ice458/pico_synthesizer/pitch_bend_table_interpolated.h

#ifndef PITCH_BEND_TABLE_INTERPOLATED_H
#define PITCH_BEND_TABLE_INTERPOLATED_H

#include "fp.h"

#define PITCH_BEND_INTERPOLATED_TABLE_SIZE 256
#define PITCH_BEND_ORIGINAL_TABLE_SIZE 16384

// Pitch bend factors (interpolated): Q8 format
// 2D Array: pitch_bend_factors_interpolated[max_semitones_0_to_24][bend_value_0_to_255]
// Dimensions: [25][256]
static const q8_t pitch_bend_factors_interpolated[25][256] = {
    { // Table for +/- 0 semitones
        256, 256, 256, 256, 256, 256, 256, 256, 
        256, 256, 256, 256, 256, 256, 256, 256, 
        256, 256, 256, 256, 256, 256, 256, 256, 
        256, 256, 256, 256, 256, 256, 256, 256, 
        256, 256, 256, 256, 256, 256, 256, 256, 
        256, 256, 256, 256, 256, 256, 256, 256, 
        256, 256, 256, 256, 256, 256, 256, 256, 
        256, 256, 256, 256, 256, 256, 256, 256, 
        256, 256, 256, 256, 256, 256, 256, 256, 
        256, 256, 256, 256, 256, 256, 256, 256, 
        256, 256, 256, 256, 256, 256, 256, 256, 
        256, 256, 256, 256, 256, 256, 256, 256, 
        256, 256, 256, 256, 256, 256, 256, 256, 
        256, 256, 256, 256, 256, 256, 256, 256, 
        256, 256, 256, 256, 256, 256, 256, 256, 
        256, 256, 256, 256, 256, 256, 256, 256, 
        256, 256, 256, 256, 256, 256, 256, 256, 
        256, 256, 256, 256, 256, 256, 256, 256, 
        256, 256, 256, 256, 256, 256, 256, 256, 
        256, 256, 256, 256, 256, 256, 256, 256, 
        256, 256, 256, 256, 256, 256, 256, 256, 
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
        670, 677, 685, 692, 700, 707, 715, 723, 
        731, 739, 747, 755, 763, 772, 780, 789, 
        797, 806, 815, 824, 833, 842, 851, 860, 
        870, 879, 889, 899, 908, 918, 928, 939, 
        949, 959, 970, 980, 991, 1002, 1013, 1024
    }
};

#endif // PITCH_BEND_TABLE_INTERPOLATED_H
