ice458/pico_synthesizer/tone.c

#include "synthesizer.h"
#include "fp.h"
#include "tone.h"

tone_t tone_gm[128] =
    {
        // GM Tone Definitions
        {{SIN}, {31, 75}, {0, 5, 90, 10, 0}, 100},       // 0 Acoustic Grand Piano
        {{TRI}, {31, 100}, {0, 5, 90, 10, 0}, 100},      // 1 Bright Acoustic Piano
        {{TRI}, {31, 127}, {0, 5, 90, 10, 0}, 100},      // 2 Electric Grand Piano
        {{SIN}, {32, 100}, {0, 15, 90, 10, 0}, 80},      // 3 Honky-tonk Piano
        {{SIN}, {95, 80}, {0, 5, 90, 10, 0}, 42},        // 4 Electric Piano 1
        {{SIN}, {127, 100}, {0, 5, 90, 10, 0}, 46},      // 5 Electric Piano 2
        {{SAW}, {63, 35}, {0, 10, 50, 8, 0}, 86},        // 6 Harpsichord
        {{SAW}, {63, 127}, {0, 10, 50, 25, 0}, 60},      // 7 Clavinet
        {{TRI}, {127, 90}, {0, 10, 50, 25, 0}, 55},      // 8 Celesta
        {{SIN}, {97, 80}, {0, 10, 50, 15, 0}, 45},       // 9 Glockenspiel
        {{SIN}, {95, 40}, {0, 15, 40, 15, 0}, 45},       // 10 Music Box
        {{SIN}, {95, 80}, {0, 10, 80, 12, 50}, 39},      // 11 Vibraphone
        {{TRI}, {127, 80}, {0, 10, 50, 33, 8}, 55},      // 12 Marimba
        {{TRI}, {63, 80}, {0, 5, 50, 80, 0}, 70},        // 13 Xylophone
        {{TRI}, {79, 45}, {0, 5, 50, 10, 0}, 70},        // 14 Tubular Bells
        {{TRI}, {79, 70}, {0, 5, 50, 30, 10}, 70},       // 15 Dulcimer
        {{SIN}, {95, 64}, {1, 2, 100, 0, 0}, 60},        // 16 Drawbar Organ
        {{SIN}, {95, 40}, {1, 20, 40, 0, 0}, 60},        // 17 Percussive Organ
        {{SIN}, {47, 80}, {1, 20, 40, 0, 0}, 46},        // 18 Rock Organ
        {{SQU}, {95, 127}, {3, 20, 80, 0, 6}, 30},       // 19 Church Organ
        {{SAW}, {95, 127}, {5, 20, 80, 0, 6}, 40},       // 20 Reed Organ
        {{SAW}, {63, 127}, {5, 20, 80, 0, 6}, 55},       // 21 Accordion
        {{SAW}, {63, 40}, {8, 20, 80, 0, 3}, 100},       // 22 Harmonica
        {{SAW}, {63, 40}, {8, 20, 80, 0, 3}, 127},       // 23 Tango Accordion
        {{TRI}, {63, 100}, {0, 3, 80, 10, 3}, 70},       // 24 Acoustic Guitar (nylon)
        {{TRI}, {63, 65}, {0, 3, 80, 10, 3}, 65},        // 25 Acoustic Guitar (steel)
        {{TRI}, {95, 100}, {0, 3, 80, 10, 3}, 65},       // 26 Electric Guitar (jazz)
        {{TRI}, {95, 65}, {0, 3, 80, 10, 3}, 60},        // 27 Electric Guitar (clean)
        {{TRI}, {95, 65}, {0, 3, 80, 52, 3}, 58},        // 28 Electric Guitar (muted)
        {{SQU}, {95, 100}, {0, 3, 80, 0, 3}, 40},        // 29 Overdriven Guitar
        {{SQU}, {79, 80}, {0, 3, 80, 0, 3}, 30},         // 30 Distortion Guitar
        {{SQU}, {31, 120}, {0, 3, 80, 5, 3}, 50},        // 31 Guitar Harmonics
        {{TRI}, {63, 120}, {0, 2, 80, 4, 3}, 70},        // 32 Acoustic Bass
        {{TRI}, {63, 40}, {0, 2, 80, 4, 3}, 90},         // 33 Electric Bass (finger)
        {{SIN}, {31, 40}, {0, 2, 80, 4, 3}, 90},         // 34 Electric Bass (pick)
        {{SAW}, {63, 120}, {0, 2, 80, 4, 3}, 75},        // 35 Fretless Bass
        {{SAW}, {63, 90}, {0, 5, 60, 4, 3}, 65},         // 36 Slap Bass 1
        {{SAW}, {63, 110}, {0, 5, 60, 4, 3}, 65},        // 37 Slap Bass 2
        {{SQU}, {63, 20}, {0, 5, 60, 4, 3}, 90},         // 38 Synth Bass 1
        {{SQU}, {63, 70}, {0, 5, 60, 4, 3}, 45},         // 39 Synth Bass 2
        {{SAW}, {63, 70}, {4, 14, 84, 0, 6}, 65},        // 40 Violin
        {{SAW}, {63, 110}, {4, 14, 84, 0, 6}, 110},      // 41 Viola
        {{SAW}, {63, 120}, {6, 14, 84, 0, 6}, 80},       // 42 Cello
        {{SAW}, {95, 127}, {8, 14, 84, 0, 6}, 60},       // 43 Contrabass
        {{SQU}, {31, 127}, {4, 14, 84, 0, 6}, 65},       // 44 Tremolo Strings
        {{SQU}, {31, 127}, {0, 14, 84, 45, 2}, 55},      // 45 Pizzicato Strings
        {{TRI}, {31, 80}, {0, 10, 60, 30, 15}, 95},      // 46 Orchestral Harp
        {{TRI}, {30, 40}, {0, 4, 30, 1, 8}, 127},        // 47 Timpani
        {{SQU}, {31, 105}, {4, 14, 84, 0, 6}, 65},       // 48 String Ensemble 1
        {{SQU}, {31, 105}, {16, 14, 84, 0, 6}, 65},      // 49 String Ensemble 2
        {{SAW}, {31, 110}, {10, 20, 80, 0, 6}, 115},     // 50 SynthStrings 1
        {{SAW}, {31, 127}, {10, 20, 80, 0, 6}, 127},     // 51 SynthStrings 2
        {{SAW}, {47, 127}, {15, 20, 80, 0, 6}, 60},      // 52 Choir Aahs
        {{SAW}, {47, 127}, {1, 8, 80, 0, 6}, 60},        // 53 Voice Oohs
        {{SAW}, {63, 127}, {1, 8, 80, 0, 6}, 60},        // 54 Synth Voice
        {{SQU}, {111, 100}, {0, 8, 80, 45, 6}, 33},      // 55 Orchestra Hit
        {{SAW}, {95, 127}, {3, 8, 80, 0, 3}, 55},        // 56 Trumpet
        {{SAW}, {127, 127}, {3, 8, 80, 0, 3}, 55},       // 57 Trombone
        {{SAW}, {127, 127}, {3, 8, 80, 0, 3}, 55},       // 58 Tuba
        {{SAW}, {63, 120}, {3, 8, 80, 0, 3}, 50},        // 59 Muted Trumpet
        {{SAW}, {31, 127}, {3, 50, 50, 0, 3}, 114},      // 60 French Horn
        {{SAW}, {47, 80}, {3, 50, 50, 0, 3}, 60},        // 61 Brass Section
        {{SAW}, {63, 90}, {3, 50, 50, 0, 3}, 68},        // 62 SynthBrass1
        {{SAW}, {63, 127}, {3, 50, 50, 0, 3}, 70},       // 63 SynthBrass2
        {{SAW}, {63, 127}, {3, 5, 70, 0, 3}, 70},        // 64 Soprano Sax
        {{SAW}, {63, 100}, {5, 13, 84, 0, 3}, 70},       // 65 Alto Sax
        {{SQU}, {63, 120}, {5, 13, 84, 0, 3}, 45},       // 66 Tenor Sax
        {{SQU}, {63, 100}, {5, 13, 84, 0, 3}, 45},       // 67 Baritone Sax
        {{SQU}, {31, 100}, {5, 13, 84, 0, 3}, 55},       // 68 Oboe
        {{SQU}, {31, 100}, {5, 13, 84, 0, 3}, 55},       // 69 English Horn
        {{TRI}, {31, 110}, {5, 13, 84, 0, 3}, 110},      // 70 Bassoon
        {{TRI}, {31, 110}, {5, 13, 84, 0, 3}, 110},      // 71 Clarinet
        {{SIN}, {31, 110}, {5, 13, 84, 0, 3}, 80},       // 72 Piccolo
        {{SIN}, {63, 50}, {5, 13, 84, 0, 3}, 52},        // 73 Flute
        {{SIN}, {63, 110}, {5, 13, 84, 0, 3}, 55},       // 74 Recorder
        {{SIN}, {63, 60}, {3, 50, 40, 0, 3}, 55},        // 75 Pan Flute
        {{SIN}, {63, 80}, {3, 50, 40, 0, 3}, 55},        // 76 Blown Bottle
        {{SIN}, {63, 100}, {2, 80, 30, 0, 3}, 55},       // 77 Shakuhachi
        {{TRI}, {63, 120}, {1, 20, 50, 0, 3}, 75},       // 78 Whistle
        {{SIN}, {63, 110}, {3, 20, 50, 0, 3}, 55},       // 79 Ocarina
        {{SQU}, {0, 0}, {0, 0, 127, 0, 0}, 30},          // 80 Lead 1 (square)
        {{SAW}, {0, 0}, {0, 0, 127, 0, 0}, 30},          // 81 Lead 2 (sawtooth)
        {{SAW}, {63, 110}, {0, 0, 127, 0, 0}, 50},       // 82 Lead 3 (calliope)
        {{SAW}, {63, 120}, {1, 25, 50, 0, 0}, 65},       // 83 Lead 4 (chiff)
        {{SQU}, {63, 120}, {1, 25, 50, 0, 0}, 45},       // 84 Lead 5 (charang)
        {{SQU}, {79, 120}, {1, 25, 50, 0, 0}, 35},       // 85 Lead 6 (voice)
        {{TRI}, {111, 100}, {1, 25, 50, 0, 0}, 45},      // 86 Lead7 (fifths)
        {{SAW}, {127, 120}, {1, 25, 50, 0, 0}, 50},      // 87 Lead8 (bass + lead)
        {{SIN}, {95, 120}, {1, 25, 35, 0, 20}, 45},      // 88 Pad1 (new age)
        {{SIN}, {95, 120}, {127, 127, 80, 0, 35}, 45},   // 89 Pad2 (warm)
        {{SQU}, {95, 50}, {0, 127, 80, 0, 8}, 40},       // 90 Pad3 (polysynth)
        {{SQU}, {95, 80}, {0, 127, 80, 0, 13}, 40},      // 91 Pad4 (choir)
        {{TRI}, {95, 80}, {50, 127, 80, 0, 13}, 60},     // 92 Pad5 (bowed)
        {{TRI}, {127, 80}, {50, 127, 80, 0, 13}, 55},    // 93 Pad6 (metallic)
        {{TRI}, {127, 100}, {6, 127, 80, 0, 13}, 55},    // 94 Pad7 (halo)
        {{SAW}, {95, 127}, {50, 127, 80, 0, 13}, 58},    // 95 Pad8 (sweep)
        {{TRI}, {1, 30}, {1, 50, 80, 0, 15}, 45},        // 96 FX1 (rain)
        {{TRI}, {79, 70}, {30, 50, 80, 0, 15}, 45},      // 97 FX2 (soundtrack)
        {{SIN}, {47, 50}, {3, 50, 70, 12, 15}, 45},      // 98 FX3 (crystal)
        {{SIN}, {63, 50}, {2, 120, 40, 0, 15}, 50},      // 99 FX4 (atmosphere)
        {{SIN}, {63, 110}, {2, 120, 40, 10, 35}, 60},    // 100 FX5 (brightness)
        {{SIN}, {95, 110}, {127, 120, 100, 10, 35}, 55}, // 101 FX6 (goblins)
        {{SIN}, {127, 110}, {2, 30, 55, 0, 25}, 45},     // 102 FX7 (echoes)
        {{SIN}, {127, 110}, {2, 30, 55, 0, 25}, 45},     // 103 FX8 (sci-fi)
        {{SIN}, {127, 127}, {0, 3, 45, 4, 15}, 55},      // 104 Sitar
        {{TRI}, {127, 127}, {0, 3, 45, 4, 13}, 55},      // 105 Banjo
        {{SAW}, {127, 120}, {0, 3, 45, 15, 50}, 55},     // 106 Shamisen
        {{SQU}, {127, 127}, {0, 3, 45, 15, 50}, 45},     // 107 Koto
        {{SQU}, {63, 127}, {0, 3, 45, 28, 18}, 45},      // 108 Kalimba
        {{SAW}, {95, 127}, {8, 3, 45, 0, 3}, 60},        // 109 Bag pipe
        {{SAW}, {127, 127}, {8, 3, 45, 0, 3}, 55},       // 110 Fiddle
        {{SAW}, {95, 100}, {8, 3, 45, 0, 3}, 60},        // 111 Shanai
        {{SIN}, {79, 100}, {0, 8, 45, 25, 35}, 45},      // 112 Tinkle Bell
        {{SIN}, {127, 100}, {0, 8, 45, 110, 6}, 45},     // 113 Agogo
        {{SIN}, {127, 110}, {0, 8, 45, 52, 5}, 45},      // 114 Steel Drums
        {{SIN}, {100, 50}, {0, 8, 45, 120, 5}, 45},      // 115 Woodblock
        {{TRI}, {20, 127}, {0, 8, 80, 127, 5}, 45},      // 116 Taiko Drum
        {{SIN}, {31, 127}, {0, 8, 80, 127, 5}, 50},      // 117 Melodic Tom
        {{SQU}, {31, 127}, {0, 8, 80, 127, 5}, 55},      // 118 Synth Drum
        {{TRI}, {31, 0}, {0, 8, 127, 0, 0}, 80},         // 119 Reverse Cymbal
        {{SQU}, {31, 127}, {3, 8, 50, 0, 5}, 60},        // 120 Guitar Fret Noise
        {{NOISE}, {0, 0}, {8, 8, 50, 127, 5}, 30},       // 121 Breath Noise
        {{NOISE}, {0, 127}, {8, 8, 50, 0, 5}, 40},       // 122 Seashore
        {{SIN}, {0, 0}, {8, 8, 50, 0, 5}, 45},           // 123 Bird Tweet
        {{SIN}, {0, 100}, {0, 0, 127, 0, 0}, 40},        // 124 Telephone Ring
        {{NOISE}, {1, 127}, {127, 0, 127, 0, 50}, 35},   // 125 Helicopter
        {{NOISE}, {3, 127}, {127, 0, 127, 0, 30}, 35},   // 126 Applause
        {{NOISE}, {10, 127}, {0, 10, 100, 40, 3}, 40}    // 127 Gunshot
};
