ice458/pico_synthesizer/wave_table.h

#ifndef WAVE_TABLE_H
#define WAVE_TABLE_H
#include <stdint.h>
#include "fp.h"
#define TABLE_LENGTH 4096
static const fp_t sin_table[] = {0,50,101,151,201,251,302,352,402,452,503,553,603,654,704,754,804,855,905,955,1005,1056,1106,1156,1206,1257,1307,1357,1407,1458,1508,1558,1608,1658,1709,1759,1809,1859,1909,1960,2010,2060,2110,2160,2210,2261,2311,2361,2411,2461,2511,2561,2612,2662,2712,2762,2812,2862,2912,2962,3012,3062,3112,3162,3213,3263,3313,3363,3413,3463,3513,3563,3613,3662,3712,3762,3812,3862,3912,3962,4012,4062,4112,4162,4212,4261,4311,4361,4411,4461,4510,4560,4610,4660,4710,4759,4809,4859,4909,4958,5008,5058,5107,5157,5207,5256,5306,5355,5405,5455,5504,5554,5603,5653,5702,5752,5801,5851,5900,5950,5999,6049,6098,6147,6197,6246,6295,6345,6394,6443,6493,6542,6591,6640,6690,6739,6788,6837,6886,6936,6985,7034,7083,7132,7181,7230,7279,7328,7377,7426,7475,7524,7573,7622,7671,7720,7768,7817,7866,7915,7964,8012,8061,8110,8159,8207,8256,8305,8353,8402,8450,8499,8547,8596,8645,8693,8741,8790,8838,8887,8935,8983,9032,9080,9128,9177,9225,9273,9321,9370,9418,9466,9514,9562,9610,9658,9706,9754,9802,9850,9898,9946,9994,10042,10090,10138,10185,10233,10281,10329,10376,10424,10472,10519,10567,10614,10662,10709,10757,10804,10852,10899,10947,10994,11041,11089,11136,11183,11231,11278,11325,11372,11419,11466,11513,11561,11608,11655,11702,11749,11795,11842,11889,11936,11983,12030,12076,12123,12170,12216,12263,12310,12356,12403,12449,12496,12542,12589,12635,12681,12728,12774,12820,12867,12913,12959,13005,13051,13098,13144,13190,13236,13282,13328,13373,13419,13465,13511,13557,13603,13648,13694,1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
