ice458/pico_synthesizer/pan_table.c

#include "pan_table.h"
#include "fp.h"

const fp_t pan_table[PAN_TABLE_SIZE][2] = {
    {32767, 0},
    {32764, 405},
    {32756, 810},
    {32744, 1215},
    {32726, 1620},
    {32704, 2025},
    {32676, 2429},
    {32644, 2833},
    {32606, 3236},
    {32564, 3639},
    {32516, 4042},
    {32464, 4444},
    {32406, 4845},
    {32344, 5245},
    {32276, 5645},
    {32204, 6044},
    {32127, 6442},
    {32045, 6839},
    {31958, 7234},
    {31866, 7629},
    {31769, 8023},
    {31667, 8415},
    {31561, 8806},
    {31450, 9196},
    {31333, 9584},
    {31212, 9971},
    {31087, 10356},
    {30956, 10740},
    {30821, 11122},
    {30681, 11502},
    {30537, 11881},
    {30387, 12258},
    {30233, 12632},
    {30075, 13005},
    {29912, 13376},
    {29744, 13745},
    {29572, 14112},
    {29395, 14477},
    {29213, 14839},
    {29028, 15199},
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
};
