ice458/pico_synthesizer/vibrato_table.h

#ifndef VIBRATO_TABLE_H
#define VIBRATO_TABLE_H
#include "fp.h"

#define VIBRATO_TABLE_LENGTH 128
static const q8_t vibrato_table[] = {131,132,134,136,138,140,142,144,145,147,149,151,153,155,157,158,160,162,164,166,168,170,171,173,175,177,179,181,183,184,186,188,190,192,194,196,197,199,201,203,205,207,209,210,212,214,216,218,220,222,223,225,227,229,231,233,235,236,238,240,242,244,246,248,249,251,253,255,257,259,261,262,264,266,268,270,272,274,275,277,279,281,283,285,287,288,290,292,294,296,298,300,301,303,305,307,309,311,313,314,316,318,320,322,324,326,327,329,331,333,335,337,339,340,342,344,346,348,350,352,353,355,357,359,361,363,365,367};
#endif // VIBRATO_TABLE_H
